oskar-ka/nixie/circuit/relax_osc.png

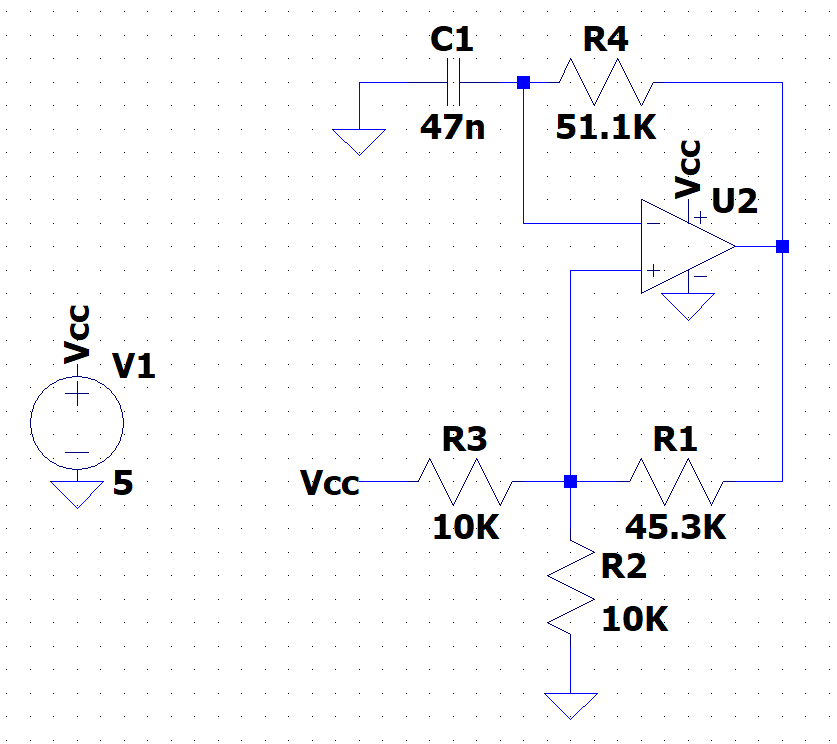
circuit/relax_osc.png
