oskar-ka/nixie/spice_simulations/2_stage_boost_converter.asc

B1: bv; V=if(V(Vcontrol)>6, 12, 0)
C1: cap; 10µ
C2: cap; 10µ
C3: cap; 10n
C4: cap; 10n
D1: diode; ES1D
D2: diode; ES1D
D3: diode; ES1D
D4: diode; ES1D
L1: ind; 100µ
L2: ind; 100µ
M1: nmos; IRF530
M2: nmos; FDS2734
R1: res; 7k25
R2: res; 9k7
R3: res; 271k
R4: res; 16k
R5: res; 5k55
R6: res; 6k45
R7: res; 10k3
R11: res; 1
U1: UniversalOpAmp2; Avol=1Meg GBW=1G Slew=1G
U2: UniversalOpAmp2; Avol=1Meg GBW=1G Slew=1G
V1: voltage; 5
V2: voltage; PWL REPEAT FOREVER(0 4 2.5u 8 5u 4) ENDREPEAT
Vs: voltage; 12; Rser=1
Named nets: 0, Vs, Vout, Vg, Vtri, 5V, Vcontrol
.tran 0 20m 0
Comparator+gate driver
Boost stage
Feedback controller
Oscillator
.ic I(L1)=0 I(L2)=0 V(C3)=0
