oskar-ka/nixie/circuit/boost_v2_nofb.asc

B1: bv; V=if(3.48>V(Vtri), 12, 0)
C1: cap; 22n; IC=2
C2: cap; 100n; IC=0
C3: cap; 1µ
C4: cap; 1µ
C5: cap; 1µ
C6: cap; 2µ
D1: diode; RFUH20NS3S
L1: ind; 3m3
Load_hi: res; 10.7k
Load_lo: res; 12.5k
M1: nmos; FDS2734
R1: res; 50k
R2: res; 25.5k
R3: res; 24.5k
R4: res; 150k
R5: res; 47
R6: res; 47
R7: res; 10K
R8: res; 10K
R9: res; 8k2
R10: res; 560
R11: res; 1
U2: UniversalOpAmp2
V1: voltage; 5
Vs: voltage; 12; Rser=1
Named nets: 0, Vs, Vout, Vcc, Vtri, Vg, Vref
.tran 0 500m 0
Comparator+gate driver
Boost stage
Oscillator
Potentiometer=50k
Soft start cap
