oskar-ka/nixie/circuit/actual_boost_converter.asc

B1: bv; V=if(3.47>V(Vtri), 12, 0)
C1: cap; 1µ
C2: cap; 470n
C3: cap; 100n
C4: cap; 22n
D1: diode; RFUH20NS3S
L1: ind; 1m6
M1: nmos; FDS2734
R1: res; 13k3
R2: res; 3k3
R3: res; 3k9
R4: res; 330k
R5: res; 5k6
R7: res; 10K
R8: res; 10K
R9: res; 8k2
R10: res; 560
R11: res; 1
R12.1: res; 330k
R12.2: res; 100k
R13: res; 10k
R14.1: res; 22k
R14.2: res; 1k8
U1: UniversalOpAmp4
U2: UniversalOpAmp2
V1: voltage; 5
Vs: voltage; 12; Rser=1
Named nets: 0, Vs, Vout, Vcc, Vfb, Vtri, Vcontrol, Vg
.tran 0 50m 0
Comparator+gate driver
Boost stage
Feedback controller
Oscillator
