oskar-ka/nixie/circuit/Draft2.asc

I1: current; 6
R1: res; 3
R2: res; 6
R3: res; 7
R4: res; 9
R5: res; 9
V1: voltage; 3
Named nets: 0
.op
