oskar-ka/nixie/circuit/relax_osc.asc

C1: cap; 22n
R1: res; 7.5k
R2: res; 10K
R3: res; 10K
R4: res; 560
U2: UniversalOpAmp2
V1: voltage; 5
Named nets: 0, Vcc
.tran 0 1m 0
