oskar-ka/nixie/circuit/boost.asc

C1: cap; 47µ
C2: cap; 47µ
D1: diode; RF04UA2D
L1: ind; 47m
M1: nmos; BSC22DN20NS3
V1: voltage; 12
V2: voltage; PULSE(0 5 22u 1u 1u 22u 45u)
Named nets: 0, in, out, control
.tran 0 1000m 0
