oskar-ka/nixie/circuit/voltage_mult.asc

C1: cap; 47µ
C2: cap; 47µ
C3: cap; 47µ
C4: cap; 47µ
C5: cap; 47µ
C6: cap; 47µ
C7: cap; 47µ
C8: cap; 47µ
C9: cap; 47µ
C10: cap; 47µ
C11: cap; 47µ
C12: cap; 47µ
C13: cap; 47µ
C14: cap; 47µ
C15: cap; 4.7µ
C16: cap; 47n; IC=2
D1: schottky; CMDSH2-3
D2: schottky; CMDSH2-3
D3: schottky; CMDSH2-3
D4: schottky; CMDSH2-3
D5: schottky; CMDSH2-3
D6: schottky; CMDSH2-3
D7: schottky; CMDSH2-3
D8: schottky; CMDSH2-3
D9: schottky; CMDSH2-3
D10: schottky; CMDSH2-3
D11: schottky; CMDSH2-3
D12: schottky; CMDSH2-3
D13: schottky; CMDSH2-3
D14: schottky; CMDSH2-3
I1: current; 20m
M1: pmos; IRF7406
M2: nmos; IRFH5302
R1: res; 10K
R2: res; 10K
R3: res; 7.5k
R4: res; 499
U1: UniversalOpAmp2; Avol=1Meg GBW=4Meg Slew=16Meg
V1: voltage; 24
V2: voltage; 5
Named nets: sqr, 0, out, Vi, Vcc
.tran 0 100m 0
