oskar-ka/nixie/circuit/regulator.asc

C1: cap; 470µ
C2: cap; 47n; IC=2
M1: nmos; BSC12DN20NS3
M2: pmos; Si1013
R1: res; 52.6k
R2: res; 806k
R3: res; 20k
R4: res; 10k
R5: res; 40k
R6: res; 20k
R7: res; 1Meg
R8: res; 499
R9: res; 10k
R10: res; 7.5k
R11: res; 10k
U1: UniversalOpAmp2
U2: UniversalOpAmp2
U3: UniversalOpAmp2
V1: voltage; 200; Rser=1500
V3: voltage; 5
V4: voltage; 24
Named nets: 0, HV, Vi, Vcc, Vout, PWM, Vgov, Vgp, Vtri, tri_inp
.tran 0 10m 0
